Tinkerforge/evse-bricklet/software/src/ads1118.c

/* evse-bricklet
 * Copyright (C) 2020 Olaf Lüke <olaf@tinkerforge.com>
 *
 * ads1118.c: ADS1118 16-Bit SPI ADC driver
 *
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
 * You should have received a copy of the GNU Lesser General Public
 * License along with this library; if not, write to the
 * Free Software Foundation, Inc., 59 Temple Place - Suite 330,
 * Boston, MA 02111-1307, USA.
 */

 // Don't fix the sign-conversion warnings in the ads1118 for now.
 // Currently this works well for WARP1 and really i don't want to touch it.
#pragma GCC diagnostic push
#pragma GCC diagnostic ignored "-Wsign-conversion"

#include "ads1118.h"
#include "configs/config_ads1118.h"

#include <stdlib.h>

#include "bricklib2/utility/util_definitions.h"
#include "bricklib2/utility/moving_average.h"
#include "bricklib2/os/coop_task.h"
#include "bricklib2/logging/logging.h"

#define ADS1118_MOVING_AVERAGE_LENGTH 4
#define ADS1118_CONFIGURE_TIMEOUT 200

#include "configs/config_evse.h"

#include "evse.h"
#include "iec61851.h"
#include "button.h"

CoopTask ads1118_task;
ADS1118 ads1118;


static void ads1118_init_spi(void) {
	ads1118.spi_fifo.channel             = ADS1118_USIC_SPI;
	ads1118.spi_fifo.baudrate            = ADS1118_SPI_BAUDRATE;

	ads1118.spi_fifo.rx_fifo_size        = ADS1118_RX_FIFO_SIZE;
	ads1118.spi_fifo.rx_fifo_pointer     = ADS1118_RX_FIFO_POINTER;
	ads1118.spi_fifo.tx_fifo_size        = ADS1118_TX_FIFO_SIZE;
	ads1118.spi_fifo.tx_fifo_pointer     = ADS1118_TX_FIFO_POINTER;

	ads1118.spi_fifo.slave               = ADS1118_SLAVE;
	ads1118.spi_fifo.clock_output        = ADS1118_CLOCK_OUTPUT;
	ads1118.spi_fifo.clock_passive_level = ADS1118_CLOCK_PASSIVE_LEVEL;

	ads1118.spi_fifo.sclk_pin            = ADS1118_SCLK_PIN;
	ads1118.spi_fifo.sclk_port           = ADS1118_SCLK_PORT;
	ads1118.spi_fifo.sclk_pin_mode       = ADS1118_SCLK_PIN_MODE;

	ads1118.spi_fifo.select_pin          = ADS1118_SELECT_PIN;
	ads1118.spi_fifo.select_port         = ADS1118_SELECT_PORT;
	ads1118.spi_fifo.select_pin_mode     = ADS1118_SELECT_PIN_MODE;

	ads1118.spi_fifo.mosi_pin            = ADS1118_MOSI_PIN;
	ads1118.spi_fifo.mosi_port           = ADS1118_MOSI_PORT;
	ads1118.spi_fifo.mosi_pin_mode       = ADS1118_MOSI_PIN_MODE;

	ads1118.spi_fifo.miso_pin            = ADS1118_MISO_PIN;
	ads1118.spi_fifo.miso_port           = ADS1118_MISO_PORT;
	ads1118.spi_fifo.miso_input          = ADS1118_MISO_INPUT;
	ads1118.spi_fifo.miso_source         = ADS1118_MISO_SOURCE;

	spi_fifo_init(&ads1118.spi_fifo);
}

// channel 0 = measure CP
// channel 1 = measure PP
// channel 2 = measure temperature
uint8_t *ads1118_get_config_for_mosi(const uint8_t channel, const bool normal) {
	static uint8_t mosi[2] = {0, 0};

	uint16_t config = 0;
	if(normal) { // normal loop
		config = ADS1118_CONFIG_SINGLE_SHOT | ADS1118_CONFIG_POWER_DOWN | ADS1118_CONFIG_GAIN_4_096V | ADS1118_CONFIG_DATA_RATE_8SPS  | ADS1118_CONFIG_PULL_UP_ENABLE | ADS1118_CONFIG_NOP;
	} else { // fast loop
		config = /* continous mode */                                     ADS1118_CONFIG_GAIN_4_096V | ADS1118_CONFIG_DATA_RATE_32SPS | ADS1118_CONFIG_PULL_UP_ENABLE | ADS1118_CONFIG_NOP;
	}

	if(channel == 3) {
		// We use channel 3 for version testing, version testing is done by measuring between IN1 and GND
		config |= ADS1118_CONFIG_INP_IS_IN1_AND_INN_IS_GND;
	} else {
		if(ads1118.is_v15) {
			switch(channel) {
				case 0: config |= ADS1118_CONFIG_INP_IS_IN1_AND_INN_IS_GND; break;
				case 1: config |= ADS1118_CONFIG_INP_IS_IN2_AND_INN_IS_IN3; break;
				case 2: config |= ADS1118_CONFIG_TEMPERATURE_MODE;          break;
				default: break;
			}
		} else {
			switch(channel) {
				case 0: config |= ADS1118_CONFIG_INP_IS_IN0_AND_INN_IS_IN3; break;
				case 1: config |= ADS1118_CONFIG_INP_IS_IN2_AND_INN_IS_IN3; break;
				case 2: config |= ADS1118_CONFIG_TEMPERATURE_MODE;          break;
				default: break;
			}
		}
	}

	mosi[0] = (config >> 8) & 0xFF;
	mosi[1] = (config >> 0) & 0xFF;
	return mosi;
}

void ads1118_cp_adc_avg_queue_add(uint16_t value) {
	ads1118.cp_adc_avg_queue[ads1118.cp_adc_avg_queue_pos] = value;
	ads1118.cp_adc_avg_queue_pos = (ads1118.cp_adc_avg_queue_pos + 1) % ADS1118_CP_ADC_AVG_NUM;
}

int ads1118_sort_compare( const void* a, const void* b) {
   uint16_t int_a = *((uint16_t*)a);
   uint16_t int_b = *((uint16_t*)b);

   return (int_a > int_b) - (int_a < int_b);
}

uint16_t ads1118_cp_adc_avg_queue_get(void) {
	uint16_t tmp[ADS1118_CP_ADC_AVG_NUM];
	memcpy(tmp, ads1118.cp_adc_avg_queue, sizeof(uint16_t)*ADS1118_CP_ADC_AVG_NUM);

	// Sort the queue
	qsort(tmp, ADS1118_CP_ADC_AVG_NUM, sizeof(uint16_t), ads1118_sort_compare);

	// Return the value at 1/3 above the median
	return tmp[ADS1118_CP_ADC_AVG_NUM*2/3];
}

void ads1118_cp_handle_continuous_calibration(const uint16_t adc_value) {
	// We don't do the calibration if the box is not enabled
	if(button.state == BUTTON_STATE_PRESSED) {
		return;
	}

	// If the adc value is below 11.75V, we ignore it.
	// We don't accept a voltage this small as max cp voltage
	const int16_t voltage = SCALE(adc_value, 6574, 31643, -12000, 12000);
	if(voltage < 11750) {
		return;
	}

	// Do continuous calibration in IEC61851 State A
	// and 500ms between state change and continuous calibration.
	if((iec61851.state == IEC61851_STATE_A) && system_timer_is_time_elapsed_ms(iec61851.last_state_change, 500)) {
		if(ads1118.moving_average_cp_adc_12v_new) {
			ads1118.moving_average_cp_adc_12v_new = false;
			moving_average_init(&ads1118.moving_average_cp_adc_12v, adc_value, ADS1118_MOVING_AVERAGE_LENGTH);
			for(uint8_t i = 0; i < ADS1118_CP_ADC_AVG_NUM; i++) {
				ads1118.cp_adc_avg_queue[i] = adc_value;
			}
		} else {
			moving_average_handle_value(&ads1118.moving_average_cp_adc_12v, adc_value);
		}

		// Take moving average
		int32_t adc_max_value_avg  = moving_average_get(&ads1118.moving_average_cp_adc_12v);

		// and put it into queue.
		ads1118_cp_adc_avg_queue_add(adc_max_value_avg);

		// From the queue we use the value a bit above the median.
		adc_max_value_avg = ads1118_cp_adc_avg_queue_get();

		// The voltage in the queue is the continuous calibrated max voltage (ADC value),
		const int16_t v = SCALE(adc_max_value_avg, 6574, 31643, -12000, 12000);

		// Apply additional ADC calibration
		if(ads1118.cp_user_cal_active) {
			ads1118.cp_cal_max_voltage = v * ads1118.cp_user_cal_mul / ads1118.cp_user_cal_div;
		} else {
			ads1118.cp_cal_max_voltage = v * ads1118.cp_cal_mul / ads1118.cp_cal_div;
		}

		// For the min voltage we use a fixed difference that is calibrated on intial flashing
		if(ads1118.cp_user_cal_active) {
			ads1118.cp_cal_min_voltage = -ads1118.cp_cal_max_voltage + ads1118.cp_user_cal_diff_voltage;
		} else {
			ads1118.cp_cal_min_voltage = -ads1118.cp_cal_max_voltage + ads1118.cp_cal_diff_voltage;
		}
	}
}

void ads1118_cp_voltage_from_miso(const uint8_t *miso) {
	ads1118.cp_adc_value = (miso[1] | (miso[0] << 8));
	ads1118_cp_handle_continuous_calibration(ads1118.cp_adc_value);

	// adc_sum and adc_sum_count is used during calibration and otherwise ignored
	ads1118.cp_adc_sum += ads1118.cp_adc_value;
	ads1118.cp_adc_sum_count++;

	// 0.8217V => -12V
	// 3.9554V =>  12V
	// 1 LSB = 125uV
	// ===>
	// 6574 LSB  => -12V
	// 31643 LSB =>  12V

	ads1118.cp_voltage = SCALE(ads1118.cp_adc_value, 6574, 31643, -12000, 12000);
	if(ads1118.cp_user_cal_active) {
		ads1118.cp_voltage_calibrated = ads1118.cp_voltage * ads1118.cp_user_cal_mul / ads1118.cp_user_cal_div;
	} else {
		ads1118.cp_voltage_calibrated = ads1118.cp_voltage * ads1118.cp_cal_mul / ads1118.cp_cal_div;
	}
	const uint16_t current_cp_duty_cycle = evse_get_cp_duty_cycle();
	ads1118.cp_high_voltage = (ads1118.cp_voltage_calibrated - ads1118.cp_cal_min_voltage)*1000/current_cp_duty_cycle + ads1118.cp_cal_min_voltage;


	// If the measured high voltage is near the calibration max voltage
	// we assume that there is no resistance
	uint32_t new_resistance;

	// When an ID.3 is connected to the WARP charger and the duty cycle is already
	// below 100% (the wallbox is ready) but the contactor is not yet activated, the
	// ID.3 somtimes generates a spike in the resistance that we measure when it
	// engages the resistor to apply 880 ohm between CP/PE. We have not seen this in
	// other cars, we assume this is some kind of capacitive effect. To make sure
	// that we don't cancel the charging here, we increase the "infinite resistance"
	// threshold for this scenario.
	const bool id3_mode = (current_cp_duty_cycle != 1000) && !XMC_GPIO_GetInput(EVSE_RELAY_PIN);
	const bool has_forced_16a = !XMC_GPIO_GetInput(EVSE_RELAY_PIN) && (current_cp_duty_cycle == 266);
	if(!has_forced_16a && id3_mode && (ads1118.cp_high_voltage + 500 > ads1118.cp_cal_max_voltage)) {
		new_resistance = 0xFFFF;
	} else if(!has_forced_16a && !id3_mode && (ads1118.cp_high_voltage + 1000 > ads1118.cp_cal_max_voltage)) {
		new_resistance = 0xFFFF;
	} else {
		// resistance divider, 910 ohm on EVSE
		// diode voltage drop 650mV (value is educated guess)
		// voltage drop of opamp under with 880 ohm load: 617mV
		if(current_cp_duty_cycle == 1000) { // w/o PWM
			if(ads1118.cp_user_cal_active) {
				if(ads1118.cp_high_voltage > (ads1118.cp_cal_max_voltage - ads1118.cp_user_cal_2700ohm)) {
					new_resistance = 0xFFFF;
				} else {
					new_resistance = 910*(ads1118.cp_high_voltage - ADS1118_DIODE_DROP)/((ads1118.cp_cal_max_voltage - ads1118.cp_user_cal_2700ohm) - ads1118.cp_high_voltage);
				}
			} else {
				if(ads1118.cp_high_voltage > (ads1118.cp_cal_max_voltage - ads1118.cp_cal_2700ohm)) {
					new_resistance = 0xFFFF;
				} else {
					new_resistance = 910*(ads1118.cp_high_voltage - ADS1118_DIODE_DROP)/((ads1118.cp_cal_max_voltage - ads1118.cp_cal_2700ohm) - ads1118.cp_high_voltage);
				}
			}
		} else { // w/ PWM
			uint32_t ma = iec61851_get_max_ma();

			uint32_t index = SCALE(ma, 6000, 32000, 0, ADS1118_880OHM_CAL_NUM-1);
			// Special handling for 16A forced mode
			if(current_cp_duty_cycle == 266) {
				index = 5;
			}
			if(ads1118.cp_user_cal_active) {
				if(ads1118.cp_high_voltage > (ads1118.cp_cal_max_voltage - ads1118.cp_user_cal_880ohm[index])) {
					new_resistance = 0xFFFF;
				} else {
					new_resistance = 910*(ads1118.cp_high_voltage - ADS1118_DIODE_DROP)/((ads1118.cp_cal_max_voltage - ads1118.cp_user_cal_880ohm[index])  - ads1118.cp_high_voltage);
				}
			} else {
				if(ads1118.cp_high_voltage > (ads1118.cp_cal_max_voltage - ads1118.cp_cal_880ohm[index])) {
					new_resistance = 0xFFFF;
				} else {
					new_resistance = 910*(ads1118.cp_high_voltage - ADS1118_DIODE_DROP)/((ads1118.cp_cal_max_voltage - ads1118.cp_cal_880ohm[index])  - ads1118.cp_high_voltage);
				}
			}
		}
		new_resistance = MIN(0xFFFF, new_resistance);
	}

	if(ads1118.moving_average_cp_new) {
		ads1118.moving_average_cp_new = false;
		moving_average_init(&ads1118.moving_average_cp, new_resistance, ADS1118_MOVING_AVERAGE_LENGTH);
	} else {
		moving_average_handle_value(&ads1118.moving_average_cp, new_resistance);
	}

	ads1118.cp_pe_resistance = moving_average_get(&ads1118.moving_average_cp);
}

void ads1118_pp_voltage_from_miso(const uint8_t *miso) {
	ads1118.pp_adc_value = (miso[1] | (miso[0] << 8));

	// 1 LSB = 125uV
	ads1118.pp_voltage = ads1118.pp_adc_value/8;

	uint32_t new_resistance;
	// If the measured high voltage is near the calibration max voltage
	// we assume that there is no resistance
	if(ABS(ads1118.pp_voltage - 4095) < 150) {
		new_resistance = 0xFFFFFFFF;
	} else {
		new_resistance = 1000*ads1118.pp_voltage/(5000 - ads1118.pp_voltage);
	}

	if(ads1118.moving_average_pp_new) {
		ads1118.moving_average_pp_new = false;
		moving_average_init(&ads1118.moving_average_pp, new_resistance, ADS1118_MOVING_AVERAGE_LENGTH);
	} else {
		moving_average_handle_value(&ads1118.moving_average_pp, new_resistance);
	}

	ads1118.pp_pe_resistance = moving_average_get(&ads1118.moving_average_pp);
}

// ADS1118 runs with 8 samples per second, so each loop takes about 250ms
uint32_t ads1118_task_normal_loop(uint32_t configure_time) {
	const XMC_GPIO_CONFIG_t config_low = {
		.mode         = XMC_GPIO_MODE_OUTPUT_PUSH_PULL,
		.output_level = XMC_GPIO_OUTPUT_LEVEL_LOW,
	};

	const XMC_GPIO_CONFIG_t config_select = {
		.mode         = ADS1118_SELECT_PIN_MODE,
		.output_level = XMC_GPIO_OUTPUT_LEVEL_LOW,
	};

	uint8_t miso[2] = {0, 0};

	// Wait for DRDY
	coop_task_sleep_ms(10);
	XMC_GPIO_Init(ADS1118_SELECT_PORT, ADS1118_SELECT_PIN, &config_low);

	configure_time = system_timer_get_ms();
	while(XMC_GPIO_GetInput(ADS1118_MISO_PORT, ADS1118_MISO_PIN)) {
		if(system_timer_is_time_elapsed_ms(configure_time, ADS1118_CONFIGURE_TIMEOUT)) {
			XMC_GPIO_Init(ADS1118_SELECT_PORT, ADS1118_SELECT_PIN, &config_select);
			spi_fifo_coop_transceive(&ads1118.spi_fifo, 2, ads1118_get_config_for_mosi(0, true), miso);
			XMC_GPIO_Init(ADS1118_SELECT_PORT, ADS1118_SELECT_PIN, &config_low);
			configure_time = system_timer_get_ms();
		}
		coop_task_yield();
	}
	XMC_GPIO_Init(ADS1118_SELECT_PORT, ADS1118_SELECT_PIN, &config_select);
	// Read CP -> Configure PP
	spi_fifo_coop_transceive(&ads1118.spi_fifo, 2, ads1118_get_config_for_mosi(1, true), miso);
	if(ads1118.cp_invalid_counter > 0) {
		ads1118.cp_invalid_counter--;
	} else {
		ads1118_cp_voltage_from_miso(miso);
	}

	// Wait for DRDY
	coop_task_sleep_ms(10);
	XMC_GPIO_Init(ADS1118_SELECT_PORT, ADS1118_SELECT_PIN, &config_low);

	configure_time = system_timer_get_ms();
	while(XMC_GPIO_GetInput(ADS1118_MISO_PORT, ADS1118_MISO_PIN)) {
		if(system_timer_is_time_elapsed_ms(configure_time, ADS1118_CONFIGURE_TIMEOUT)) {
			XMC_GPIO_Init(ADS1118_SELECT_PORT, ADS1118_SELECT_PIN, &config_select);
			spi_fifo_coop_transceive(&ads1118.spi_fifo, 2, ads1118_get_config_for_mosi(1, true), miso);
			XMC_GPIO_Init(ADS1118_SELECT_PORT, ADS1118_SELECT_PIN, &config_low);
			configure_time = system_timer_get_ms();
		}
		coop_task_yield();
	}
	XMC_GPIO_Init(ADS1118_SELECT_PORT, ADS1118_SELECT_PIN, &config_select);
	// Read PP -> Configure CP
	spi_fifo_coop_transceive(&ads1118.spi_fifo, 2, ads1118_get_config_for_mosi(0, true), miso);
	if(ads1118.pp_invalid_counter > 0) {
		ads1118.pp_invalid_counter--;
	} else {
		ads1118_pp_voltage_from_miso(miso);
	}

	return configure_time;
}

// ADS1118 runs with 32 samples per second, so each loop takes about 31.25ms
uint32_t ads1118_task_fast_loop(uint32_t configure_time) {
	const XMC_GPIO_CONFIG_t config_low = {
		.mode         = XMC_GPIO_MODE_OUTPUT_PUSH_PULL,
		.output_level = XMC_GPIO_OUTPUT_LEVEL_LOW,
	};

	const XMC_GPIO_CONFIG_t config_select = {
		.mode         = ADS1118_SELECT_PIN_MODE,
		.output_level = XMC_GPIO_OUTPUT_LEVEL_LOW,
	};

	uint8_t miso[2] = {0, 0};

	// Wait for DRDY
	coop_task_sleep_ms(1);
	XMC_GPIO_Init(ADS1118_SELECT_PORT, ADS1118_SELECT_PIN, &config_low);

	configure_time = system_timer_get_ms();
	while(XMC_GPIO_GetInput(ADS1118_MISO_PORT, ADS1118_MISO_PIN)) {
		if(system_timer_is_time_elapsed_ms(configure_time, ADS1118_CONFIGURE_TIMEOUT)) {
			XMC_GPIO_Init(ADS1118_SELECT_PORT, ADS1118_SELECT_PIN, &config_select);
			spi_fifo_coop_transceive(&ads1118.spi_fifo, 2, ads1118_get_config_for_mosi(0, false), miso);
			XMC_GPIO_Init(ADS1118_SELECT_PORT, ADS1118_SELECT_PIN, &config_low);
			configure_time = system_timer_get_ms();
		}
		coop_task_yield();
	}
	XMC_GPIO_Init(ADS1118_SELECT_PORT, ADS1118_SELECT_PIN, &config_select);

	// Read / Configure CP
	spi_fifo_coop_transceive(&ads1118.spi_fifo, 2, ads1118_get_config_for_mosi(0, false), miso);
	if(ads1118.cp_invalid_counter > 0) {
		ads1118.cp_invalid_counter--;
	} else {
		ads1118_cp_voltage_from_miso(miso);
	}

	return configure_time;
}

uint32_t ads1118_task_fast_find_version(uint32_t configure_time) {
	const XMC_GPIO_CONFIG_t config_low = {
		.mode         = XMC_GPIO_MODE_OUTPUT_PUSH_PULL,
		.output_level = XMC_GPIO_OUTPUT_LEVEL_LOW,
	};

	const XMC_GPIO_CONFIG_t config_select = {
		.mode         = ADS1118_SELECT_PIN_MODE,
		.output_level = XMC_GPIO_OUTPUT_LEVEL_LOW,
	};

	uint8_t miso[2] = {0, 0};

	// Wait for DRDY
	coop_task_sleep_ms(1);
	XMC_GPIO_Init(ADS1118_SELECT_PORT, ADS1118_SELECT_PIN, &config_low);

	configure_time = system_timer_get_ms();
	while(XMC_GPIO_GetInput(ADS1118_MISO_PORT, ADS1118_MISO_PIN)) {
		if(system_timer_is_time_elapsed_ms(configure_time, ADS1118_CONFIGURE_TIMEOUT)) {
			XMC_GPIO_Init(ADS1118_SELECT_PORT, ADS1118_SELECT_PIN, &config_select);
			spi_fifo_coop_transceive(&ads1118.spi_fifo, 2, ads1118_get_config_for_mosi(3, true), miso);
			XMC_GPIO_Init(ADS1118_SELECT_PORT, ADS1118_SELECT_PIN, &config_low);
			configure_time = system_timer_get_ms();
		}
		coop_task_yield();
	}
	XMC_GPIO_Init(ADS1118_SELECT_PORT, ADS1118_SELECT_PIN, &config_select);

	// Read / Configure CP
	spi_fifo_coop_transceive(&ads1118.spi_fifo, 2, ads1118_get_config_for_mosi(3, true), miso);
	if(ads1118.cp_invalid_counter > 0) {
		ads1118.cp_invalid_counter--;
	} else {
		// To find out if the EVSE is hardware version 1.5 we measure between IN1 und GND.
		// In version 1.4 and lower in1 is connected to GND and we will measure something near 0.
		// In version 1.5 in1 is used for the CP/PE measurement and we expect a value > 0.
		const uint16_t in1_vs_gnd = (miso[1] | (miso[0] << 8));
		ads1118.is_v15            = in1_vs_gnd > 128;
		ads1118.version_found     = true;

		// Invalidate the next measurement on both channels,
		// to make sure that this can't be mixed up with the version test measurements
		ads1118.pp_invalid_counter = MAX(ads1118.pp_invalid_counter, 1);
		ads1118.cp_invalid_counter = MAX(ads1118.cp_invalid_counter, 1);
	}

	return configure_time;
}

void ads1118_task_tick(void) {
	uint8_t miso[2] = {0, 0};

	// Configure for find version
	spi_fifo_coop_transceive(&ads1118.spi_fifo, 2, ads1118_get_config_for_mosi(3, true), miso);

	uint32_t configure_time = 0;

	while(true) {
		// Switch between normal loop and fast loop depending on IEC61851 state.
		// When we are in state C, the standard says that we have to turn the
		// contactor off within at most 100ms!
		// With the normal loop we have an ADC integration time of 250ms, so we
		// can't possibly react fast enough.
		// To fix this we have a "fast loop" that is used in state C.
		// The fast loop measures with an integration time of ~31ms and it only
		// measures the voltage between CP/PE.
		// The voltage between PP/PE is ignored (the cable obviously can't be
		// changed out while a car is charging, so it is save to ignore the
		// PP/PE voltage while in state C).
		if(ads1118.version_found) {
			if(XMC_GPIO_GetInput(EVSE_RELAY_PIN)) {
				configure_time = ads1118_task_fast_loop(configure_time);
			} else {
				configure_time = ads1118_task_normal_loop(configure_time);
			}
		} else {
			configure_time = ads1118_task_fast_find_version(configure_time);
		}

		coop_task_yield();
	}
}

void ads1118_init(void) {
	// Temporarily save calibration
	int16_t tmp_diff = ads1118.cp_cal_diff_voltage;
	int16_t tmp_div  = ads1118.cp_cal_div;
	int16_t tmp_mul  = ads1118.cp_cal_mul;
	int16_t tmp_2700 = ads1118.cp_cal_2700ohm;
	int16_t tmp_880[ADS1118_880OHM_CAL_NUM];
	memcpy(tmp_880, ads1118.cp_cal_880ohm, ADS1118_880OHM_CAL_NUM*sizeof(int16_t));

	bool tmp_user_active  = ads1118.cp_user_cal_active;
	int16_t tmp_user_diff = ads1118.cp_user_cal_diff_voltage;
	int16_t tmp_user_div  = ads1118.cp_user_cal_div;
	int16_t tmp_user_mul  = ads1118.cp_user_cal_mul;
	int16_t tmp_user_2700 = ads1118.cp_user_cal_2700ohm;
	int16_t tmp_user_880[ADS1118_880OHM_CAL_NUM];
	memcpy(tmp_user_880, ads1118.cp_user_cal_880ohm, ADS1118_880OHM_CAL_NUM*sizeof(int16_t));

	memset(&ads1118, 0, sizeof(ADS1118));

	ads1118.cp_cal_diff_voltage           = tmp_diff;
	ads1118.cp_cal_div                    = tmp_div;
	ads1118.cp_cal_mul                    = tmp_mul;
	ads1118.cp_cal_2700ohm                = tmp_2700;
	memcpy(ads1118.cp_cal_880ohm, tmp_880, ADS1118_880OHM_CAL_NUM*sizeof(int16_t));

	ads1118.cp_user_cal_active            = tmp_user_active;
	ads1118.cp_user_cal_diff_voltage      = tmp_user_diff;
	ads1118.cp_user_cal_div               = tmp_user_div;
	ads1118.cp_user_cal_mul               = tmp_user_mul;
	ads1118.cp_user_cal_2700ohm           = tmp_user_2700;
	memcpy(ads1118.cp_user_cal_880ohm, tmp_user_880, ADS1118_880OHM_CAL_NUM*sizeof(int16_t));

	ads1118.cp_cal_max_voltage            = 12193;  // Set some sane default values for min/max voltages.
	ads1118.cp_cal_min_voltage            = -12289; // These will be overwritten by continuous calibration later on.
	ads1118.moving_average_cp_adc_12v_new = true;
	ads1118.moving_average_cp_new         = true;
	ads1118.moving_average_pp_new         = true;

	ads1118_init_spi();
	coop_task_init(&ads1118_task, ads1118_task_tick);
}

void ads1118_tick(void) {
	coop_task_tick(&ads1118_task);
}

#pragma GCC diagnostic pop
